ikatkov/battery-simulator/ltspice/main-my-mod1.asc

C1: cap; 1n
C3: cap; 10µ
C4: cap; 100n
C5: cap; 1µ
C8: cap; 100n
D1: LED
D2: diode
D3: LED
D4: zener; BZX84B6V8LY
D5: zener; BZX84B6V8LY
D6: diode
D7: diode
M2: pmos; NDP6020P
Q2: npn; 2N3904
R1: res; 200
R2: res; 0.1m
R3: res; 1k
R4: res; 1
R5: res; 1k
R6: res; 2k
R7: res; 2k
R10: res; 5k
R11: res; 10
R12: res; 10k
R13: res; 1k
R14: res; 5k
R15: res; 2k
R16: res; 1k
R17: res; 1k
U1: tl431
U2: opamp2; LM358_AB
U3: opamp2; LM358_AB
U4: opamp2; LM358_AB
U5: tip142
V1: voltage; 12
V2: voltage; 24
V3: voltage; 2
Named nets: 0, VCC, V1, V2, ref, 2.5V
.tran 0 1 10m
.inc LM358_AB.sub
.inc TL431.lib
Source
max discharge 100mA
DISCHARGE
3.5W
10k pot
10k for SD*
0.27W
sets max charge current
1V = 1A
Charger
2W
Vin must be same or higher
than charger voltage
.inc NDP6020P.lib
1W
max voltage is 
termally limited by M2
min voltage 12V
max voltage 30V
sets battery max voltage
3A schottky
3A
