ikatkov/battery-simulator/ltspice/analog-fan-control.asc

C2: cap; 5µ
D1: zener; UDZV11B
R1: res; 50k
R2: res; 2.1k
R3: res; 10Meg
R4: res; 470k
R5: res; 10k
R6: res; 67
R7: res; 470k
U1: regulators
U2: opamp2; LM358_AB
V1: voltage; 22
Named nets: 0, out
NTC
10k @ 25
2.5k @ 60
.inc LM358_AB.sub
.tran 0 600 0 startup
11V
